jonsag/avrComponentTester/Documents/PCB_mega328_ST7735/Image1.jpg

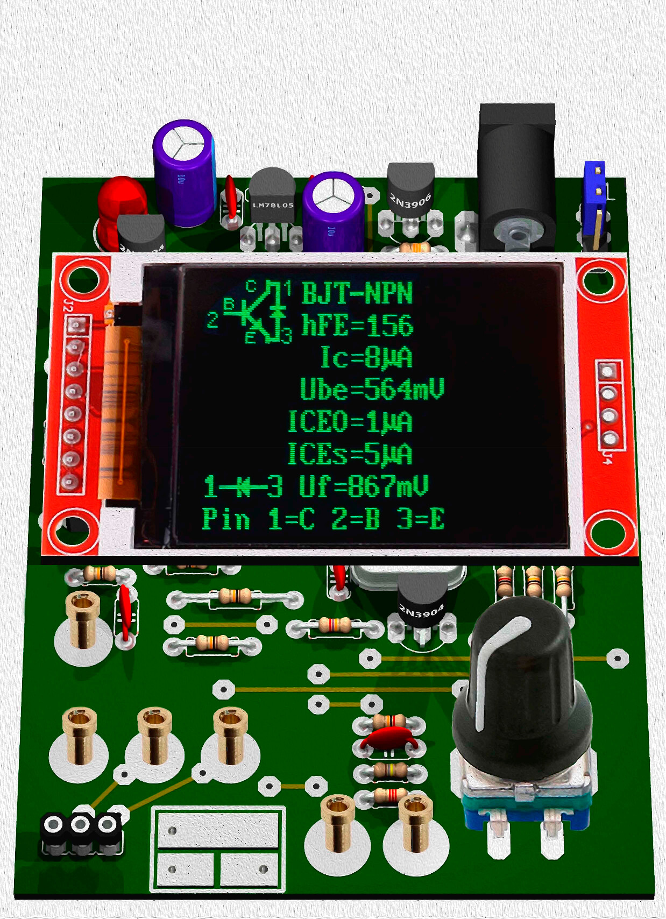
Documents/PCB_mega328_ST7735/Image1.jpg
