jonsag/avrComponentTester/avrComponentTester.asc

C1: polcap; 10µ; V=16 Irms=460m Rser=0.16 Lser=0
C2: cap; 0.1µ; V=4 Irms=0 Rser=0 Lser=0 mfg="Murata" pn="GRM011R60G103KE01" type="X5R"
C3: polcap; 10µ; V=16 Irms=2.44949 Rser=0.045 Lser=0
C4: cap; 0.1µ; V=25 Irms=0 Rser=0.00799935 Lser=255.135p
C5: polcap; 10n; V=16 Irms=0 Rser=11 Lser=0
D1: schottky; BAT54
D2: LED; STW8B12C
Q1: pnp; 2N3906
Q2: npn; 2N3904
Q3: npn; 2N3904
R1: res; 33k
R2: res; 3r3
R3: res; 100k; tol=5 pwr=0.25
R4: res; 27k; tol=5 pwr=0.25
R5: res; 27k; tol=5 pwr=0.25
R6: res; 10k; tol=5 pwr=0.25
R8: res; 10k; tol=5 pwr=0.25
U2: LT1021-5
V1: voltage; 12; Rser=0.1
Named nets: 5vOut, 0, Vin, 5V, DiodeIn, Reg.In, PD6, PD7
.tran 0.1
